Mark-MDO47/UniRemote/resources/KiCad/RFIDwriter/RFIDwriter.kicad_sch

## KiCad design resources/KiCad/RFIDwriter/RFIDwriter.kicad_sch (2025-05-08, an earlier design)

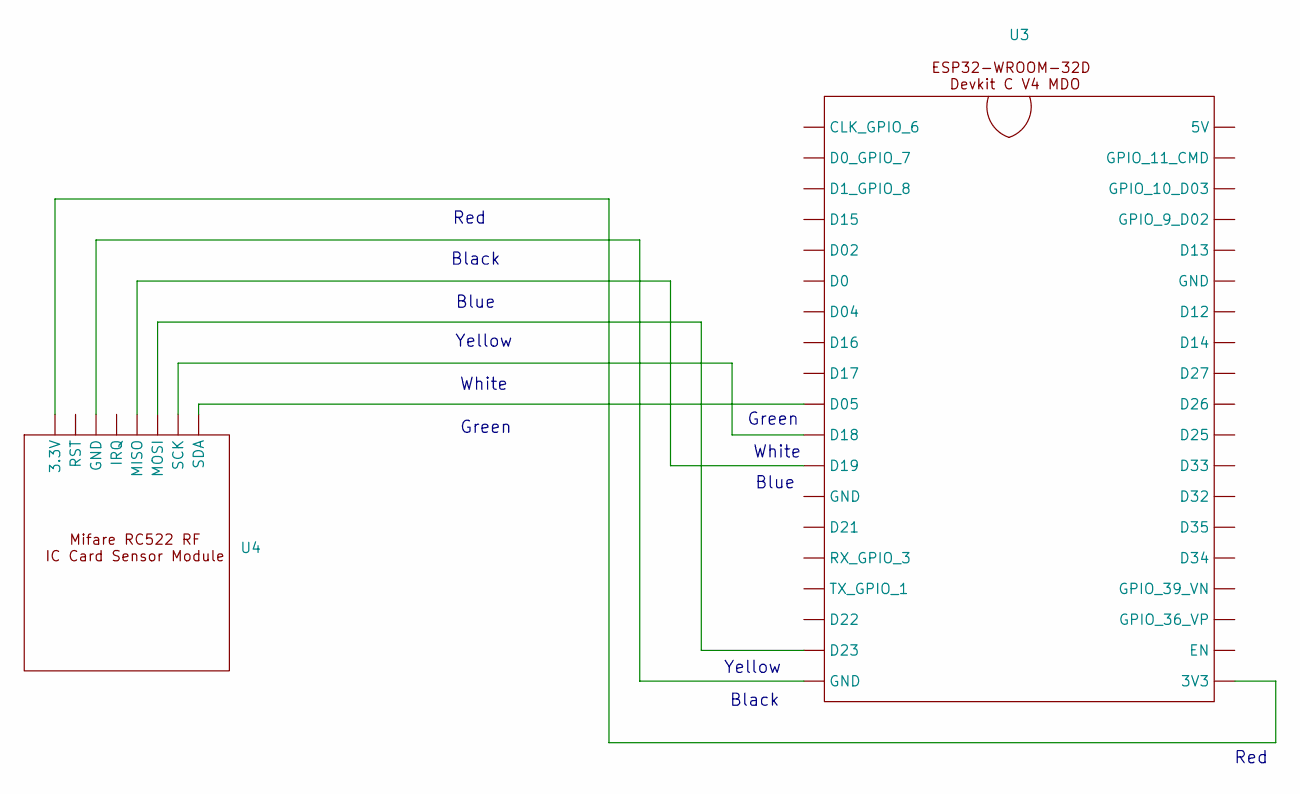
[picture p22: schematic RFIDwriter.kicad_sch]

Parts:
U3, U4: (no value)

Connections:
unnamed: U3., U4.

Notes on the sheet:
Red
Black
Blue
Green
Yellow
White
