Mark-MDO47/UniRemote/resources/KiCad/UniRemoteCYD/Battery_Power.kicad_sch

## KiCad design resources/KiCad/UniRemoteCYD/Battery_Power.kicad_sch (2025-08-08, an earlier design)

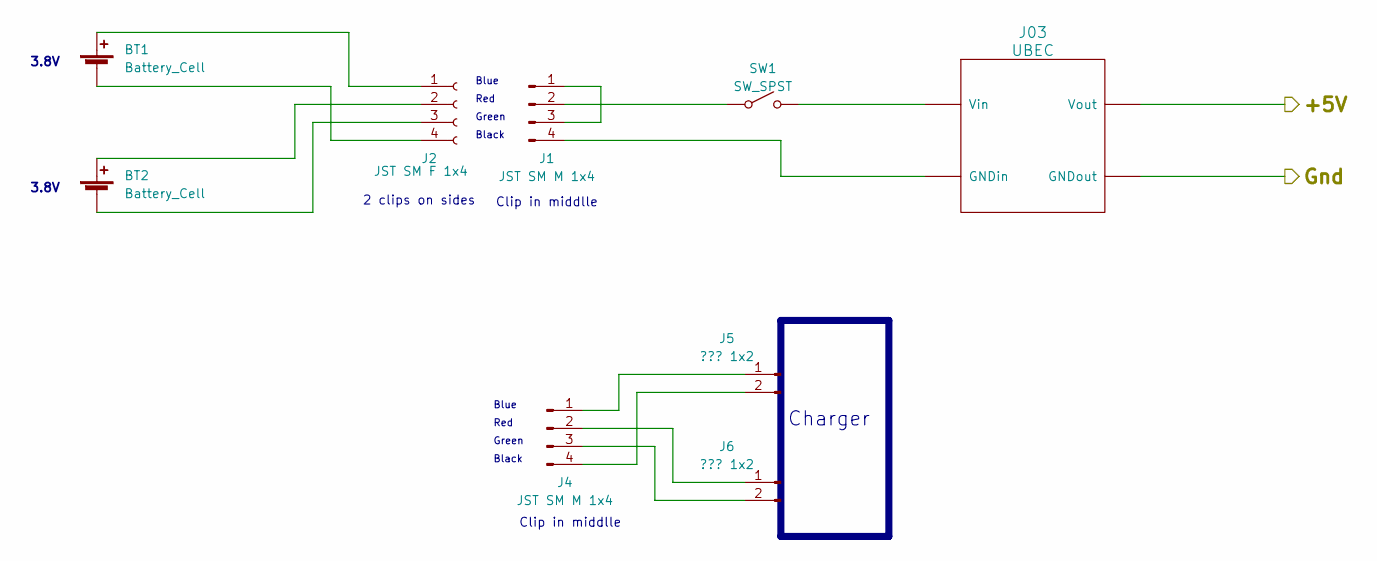
[picture p23: schematic Battery_Power.kicad_sch]

Parts:
BT1, BT2: Battery_Cell
J1, J4: JST SM M 1x4
J2: JST SM F 1x4
J03: UBEC
J5, J6: ??? 1x2
SW1: SW_SPST

Connections:
+5V: J03.~
Gnd: J03.~
unnamed: BT1.1 (+), J2.1
unnamed: BT1.2 (-), J2.4
unnamed: BT2.1 (+), J2.2
unnamed: BT2.2 (-), J2.3
unnamed: J1.1, J1.3
unnamed: J1.2, SW1.~
unnamed: J1.4, J03.~, SW1.~
unnamed: J4.1, J5.1
unnamed: J4.2, J6.1
unnamed: J4.3, J6.2
unnamed: J4.4, J5.2

Notes on the sheet:
Charger
Black
Clip in middlle
Green
Blue
3.8V
2 clips on sides
Red
