Mark-MDO47/UniRemote/resources/KiCad/UniRemoteCYD/UniRemoteCYD.kicad_sch

## KiCad design resources/KiCad/UniRemoteCYD/UniRemoteCYD.kicad_sch (2025-08-08, an earlier design)

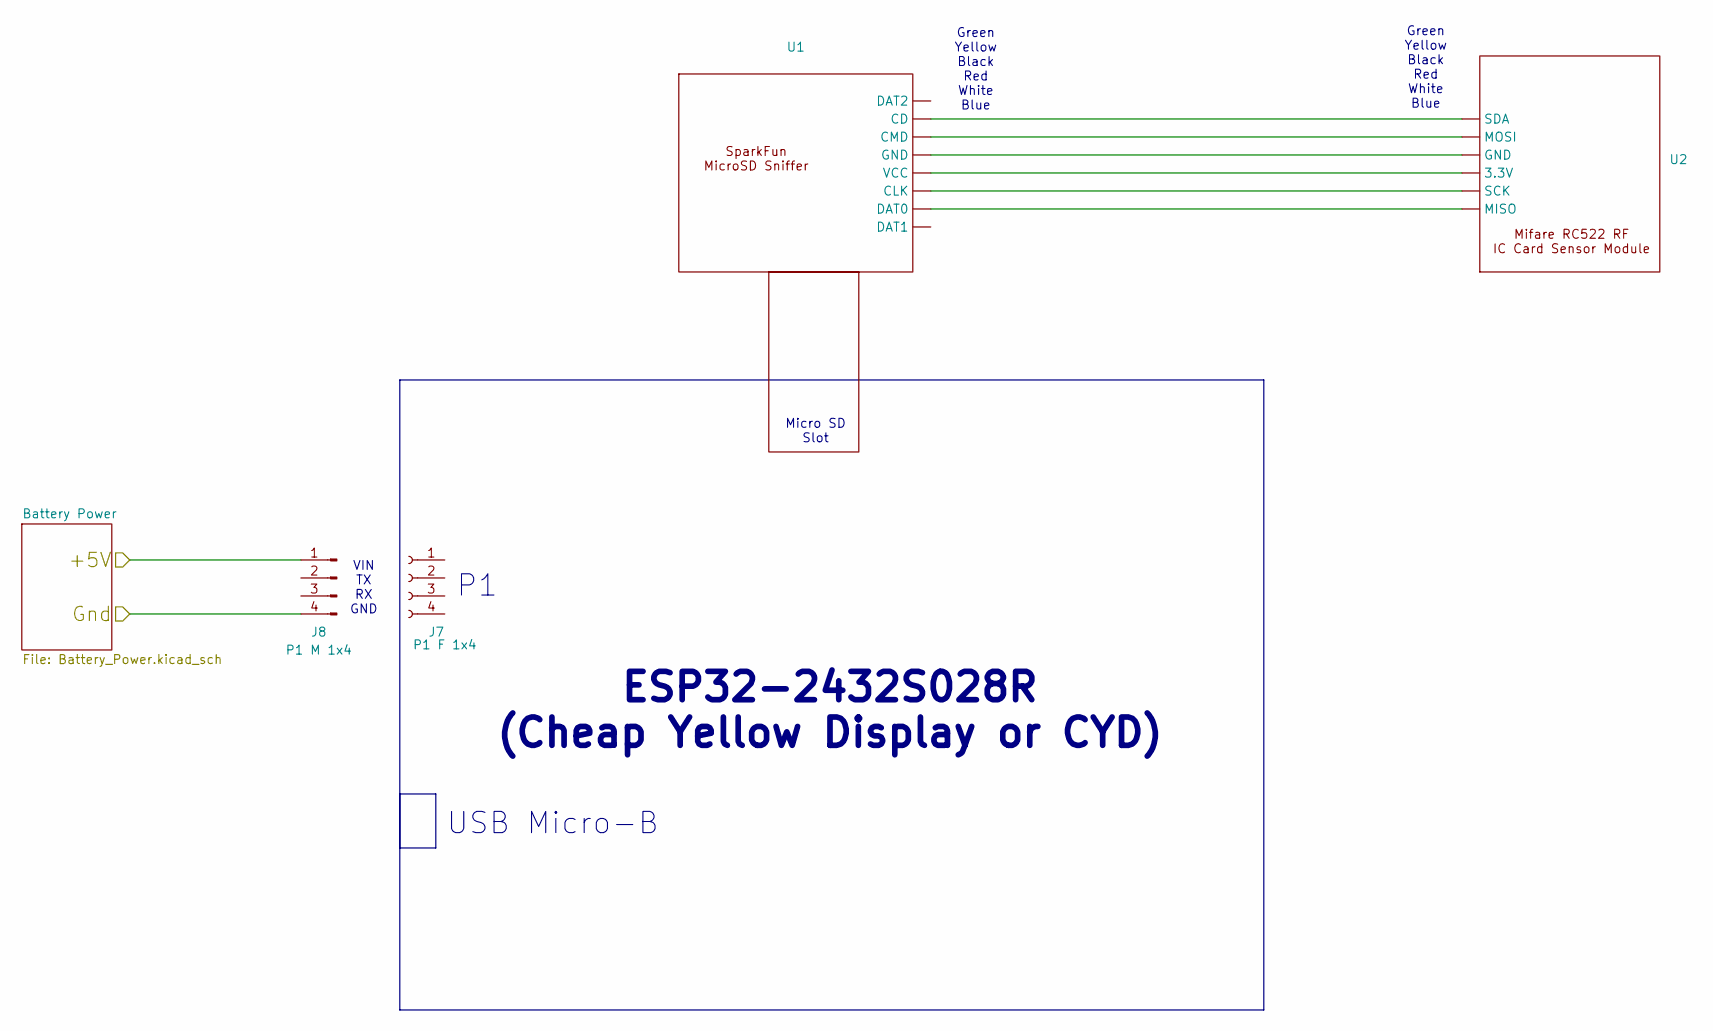
[picture p24: schematic UniRemoteCYD.kicad_sch]

Parts:
J7: P1 F 1x4
J8: P1 M 1x4
U1, U2: (no value)

Connections:
+5V: J8.1
Gnd: J8.4
unnamed: U1., U2.

Notes on the sheet:
Green Yellow Black Red White Blue
ESP32-2432S028R (Cheap Yellow Display or CYD)
VIN TX RX GND
Micro SD Slot
USB Micro-B
